docteurzoidberg/esphome-alarm-keypad/drawings/protoboards.png

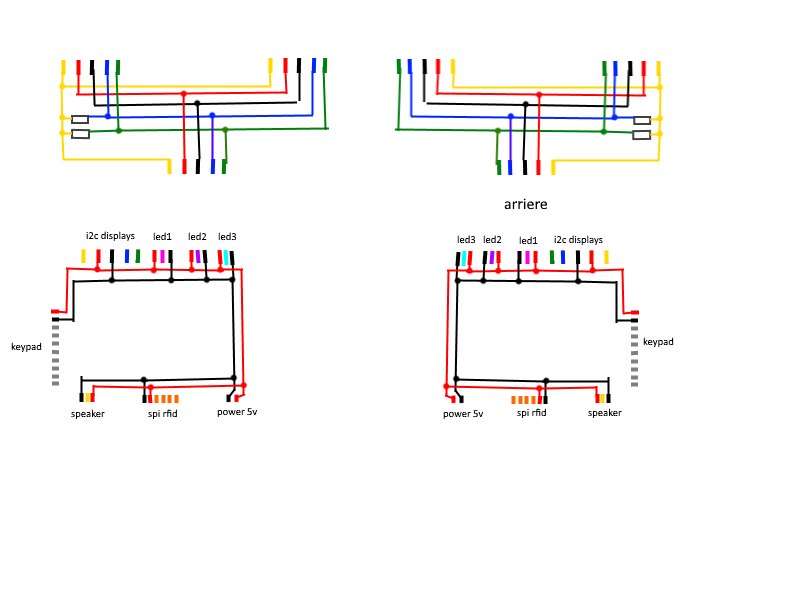
drawings/protoboards.png
