docteurzoidberg/esphome-alarm-keypad/drawings/side1.png

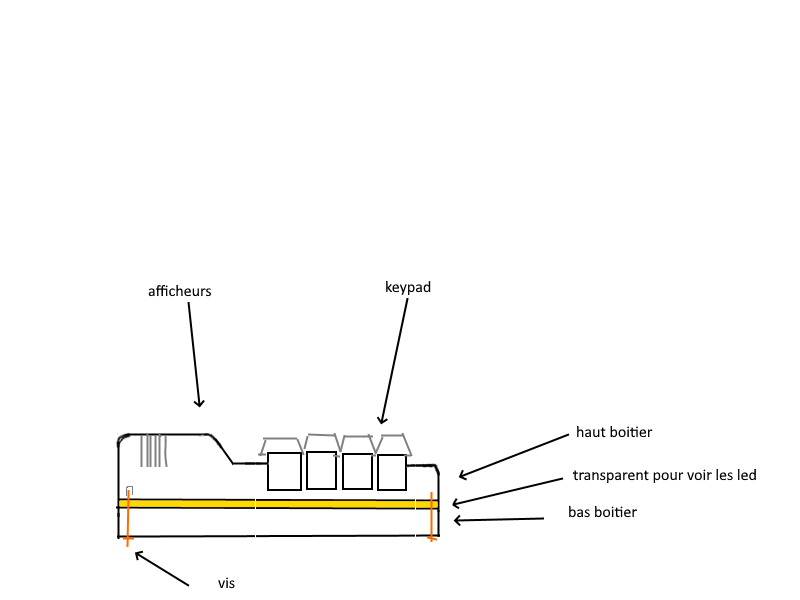
drawings/side1.png
