docteurzoidberg/esphome-alarm-keypad/pictures/2021-01-17_19-39-33.png

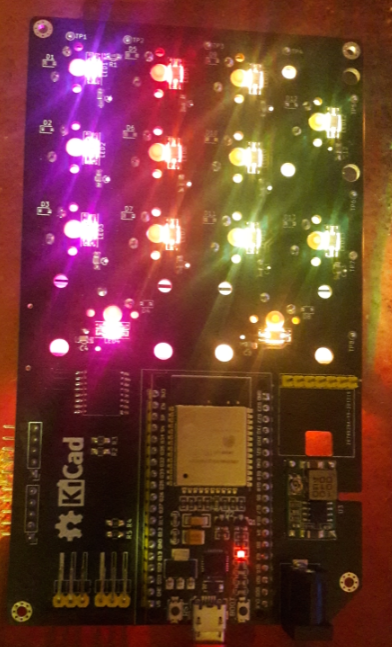
pictures/2021-01-17_19-39-33.png
