docteurzoidberg/esphome-alarm-keypad/pictures/2021-01-25_00-14-13.png

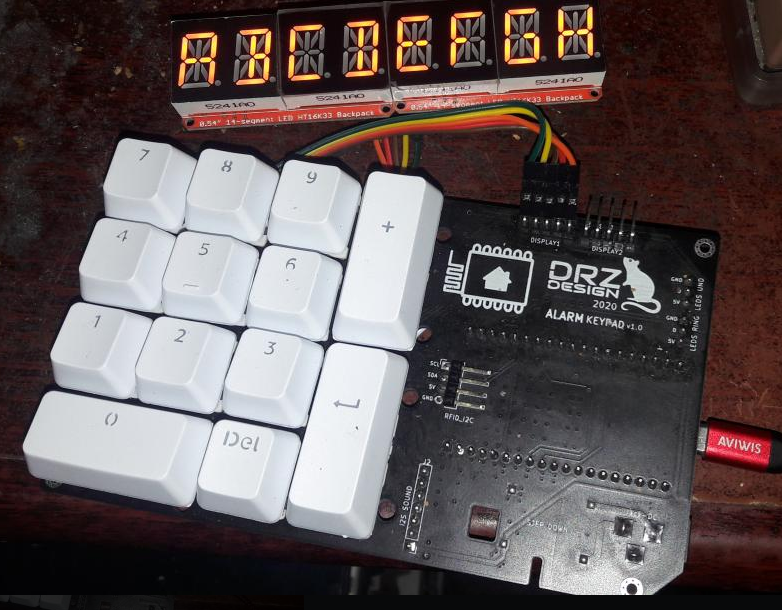
pictures/2021-01-25_00-14-13.png
